mistic100/heater-controller/firmware/src/Config.hpp

#pragma once

#include <ArduinoJson.h>
#include <LittleFS.h>

#include "constants.h"
#include "model.hpp"
#include "utils.hpp"

typedef struct
{
    bool valid;
    String line1;
    String line2;
} Lines;

class Config
{
private:
    String _wifi_ssid;
    String _wifi_pass;
    String _auth_user;
    String _auth_pass;
    Zone _zone1;
    Zone _zone2;
    Water _water;

public:
    Config() {}

    const char *wifi_ssid() const
    {
        return _wifi_ssid.c_str();
    }

    const char *wifi_pass() const
    {
        return _wifi_pass.c_str();
    }

    const char *auth_user() const
    {
        return _auth_user.c_str();
    }

    const char *auth_pass() const
    {
        return _auth_pass.c_str();
    }

    const Zone &zone1() const
    {
        return _zone1;
    }

    const Zone &zone2() const
    {
        return _zone2;
    }

    const Water &water() const
    {
        return _water;
    }

    bool save()
    {
        File file = LittleFS.open(CONFIG_FILE, FILE_WRITE);
        if (!file)
        {
            error("Failed to open config file for writing");
            return false;
        }

        JsonDocument data;
        JsonObject zone1_data = data[KEY_ZONE1].to<JsonObject>();
        serialize(_zone1, zone1_data);
        JsonObject zone2_data = data[KEY_ZONE2].to<JsonObject>();
        serialize(_zone2, zone2_data);
        JsonObject water_data = data[KEY_WATER].to<JsonObject>();
        serialize(_water, water_data);

        size_t s = serializeJson(data, file);
        file.close();

        if (s == 0)
        {
            error("Failed to write config file");
            return false;
        }
        else
        {
            info("Saved config file");
            return true;
        }
    }

    bool load()
    {
        File file = LittleFS.open(CONFIG_FILE);
        if (!file || file.size() == 0)
        {
            info("config file not found, creating a new one");
            init();
            return save();
        }
        else
        {
            info("Read config file");

            JsonDocument data;
            auto nok = deserializeJson(data, file);
            if (nok)
            {
                error("Config file invalid");
            }
            else
            {
                deserialize(_zone1, data[KEY_ZONE1]);
                deserialize(_zone2, data[KEY_ZONE2]);
                deserialize(_water, data[KEY_WATER]);
            }

            file.close();
            return !nok;
        }
    }

    void set(const JsonVariant &json)
    {
        JsonObjectConst data = json.as<JsonObjectConst>();
        deserialize(_zone1, data[KEY_ZONE1]);
        deserialize(_zone2, data[KEY_ZONE2]);
        deserialize(_water, data[KEY_WATER]);
        save();
    }

    bool loadWifi()
    {
        Lines res = readFileTwoLines(WIFI_CONFIG_FILE);
        if (!res.valid)
        {
            return false;
        }
        else
        {
            _wifi_ssid = res.line1;
            _wifi_pass = res.line2;
            return true;
        }
    }

    bool loadAuth()
    {
        Lines res = readFileTwoLines(AUTH_CONFIG_FILE);
        if (!res.valid)
        {
            return false;
        }
        else
        {
            _auth_user = res.line1;
            _auth_pass = res.line2;
            return true;
        }
    }

    bool saveWifi(const String ssid, const String pass)
    {
        if (ssid.isEmpty() || pass.isEmpty())
        {
            error("Invalid ssid/password");
            return false;
        }

        _wifi_ssid = ssid;
        _wifi_pass = pass;

        return writeFileTwoLines(WIFI_CONFIG_FILE, _wifi_ssid, _wifi_pass);
    }

    bool saveAuth(const String user, const String pass)
    {
        if (user.isEmpty() || pass.isEmpty())
        {
            error("Invalid user/password");
            return false;
        }

        _auth_user = user;
        _auth_pass = pass;

        return writeFileTwoLines(AUTH_CONFIG_FILE, _auth_user, _auth_pass);
    }

    bool saveAll()
    {
        return save() && saveWifi(_wifi_ssid, _wifi_pass) && saveAuth(_auth_user, _auth_pass);
    }

private:
    void init()
    {
        _zone1.mode = AUTO;
        _zone1.weekday.push_back({0, OFF});
        _zone1.weekend.push_back({0, OFF});
        _zone2.mode = AUTO;
        _zone2.weekday.push_back({0, OFF});
        _zone2.weekend.push_back({0, OFF});
        _water.mode = AUTO;
        _water.week.push_back({0, OFF});
    }

    void deserialize(Zone &zone, const JsonObjectConst &data)
    {
        zone.mode = strToMode(data["mode"]);
        deserialize(zone.weekday, data["weekday"].as<JsonArrayConst>());
        deserialize(zone.weekend, data["weekend"].as<JsonArrayConst>());
    }

    void deserialize(Water &water, const JsonObjectConst &data)
    {
        water.mode = strToMode(data["mode"]);
        deserialize(water.week, data["week"].as<JsonArrayConst>());
    }

    void deserialize(std::vector<TimeItem> &items, const JsonArrayConst &data)
    {
        items.clear();
        for (size_t i = 0; i < data.size(); i++)
        {
            items.push_back({(u8_t)data[i]["hour"], strToMode(data[i]["mode"])});
        }
    }

    void serialize(const Zone &zone, JsonObject &data)
    {
        data["mode"] = modeToStr(zone.mode);
        JsonArray weekday_data = data["weekday"].to<JsonArray>();
        serialize(zone.weekday, weekday_data);
        JsonArray weekend_data = data["weekend"].to<JsonArray>();
        serialize(zone.weekend, weekend_data);
    }

    void serialize(const Water &water, JsonObject &data)
    {
        data["mode"] = modeToStr(water.mode);
        JsonArray week_data = data["week"].to<JsonArray>();
        serialize(water.week, week_data);
    }

    void serialize(const std::vector<TimeItem> &items, JsonArray &data)
    {
        for (uint i = 0; i < items.size(); i++)
        {
            data[i]["hour"] = items[i].hour;
            data[i]["mode"] = modeToStr(items[i].mode);
        }
    }

    Lines readFileTwoLines(const char *path)
    {
        debug("Read file", path);

        File file = LittleFS.open(path);
        if (!file || file.size() == 0)
        {
            info("File not found");
            return {false};
        }

        String line1 = file.readStringUntil('\n');
        String line2 = file.readStringUntil('\n');
        file.close();

        if (line1.isEmpty() || line2.isEmpty())
        {
            error("File is empty or invalid");
            return {false};
        }

        return {true, line1, line2};
    }

    bool writeFileTwoLines(const char *path, const String &line1, const String &line2)
    {
        debug("Write file", path);

        File file = LittleFS.open(path, FILE_WRITE);
        if (!file)
        {
            error("Failed to open file for writing");
            return false;
        }

        bool ok = file.print(line1);
        if (ok)
            ok = file.print('\n');
        if (ok)
            ok = file.print(line2);
        if (ok)
            ok = file.print('\n');

        file.close();

        if (!ok)
        {
            error("Failed to write file");
        }

        return ok;
    }
};
